fanff/coco/3dmodels/base_plate.scad

// Coco — base plate (hip MG90S pockets + Pi Zero W + wiring).
// Print floor down.
include <coco.scad>
coco_base_print();
