fanff/coco/3dmodels/coco.scad

// Coco biped — printable parts for 4× MG90S (2 per leg) + electronics deck.
// Units: millimetres. Robot frame: +X forward, +Y left, +Z up.
//
// side = +1 → left, side = −1 → right (mirror of the left solid).

include <mg90s.scad>

$fn = $fn ? $fn : 48;
eps = 0.08;

// --- layout ---
hip_span     = 72.0;   // hip shaft to hip shaft (Y)
hip_x        = 36.0;   // hip shafts forward of plate centre
leg_len      = 56.0;   // hip shaft to foot-servo shaft (Z)
wall         = 3.6;
clearance    = 0.40;

// --- foot (MG90S laid in the sole, shaft pointing backward / −X) ---
sole_t       = 4.0;
toe_reach    = 43.0;   // forward-most toe centre, from the shaft
heel_lip     = 2.0;    // keep the heel short so the shin flange clears
foot_boss_h  = 6.5;
foot_boss_d  = 22.0;
ankle_h      = MG90S_BODY_W / 2 + clearance + wall + sole_t;

// Well footprint in foot XY after mg90s_orient_foot (left foot, shaft at origin).
function coco_foot_well_xmin() = -wall;
function coco_foot_well_xmax() = mg90s_horn_z() + wall;
function coco_foot_well_ymin() = mg90s_body_xmin() - wall;
function coco_foot_well_ymax() = mg90s_body_xmax() + wall;
function coco_foot_sole_x() = (coco_foot_well_xmin() + coco_foot_well_xmax()) / 2;
function coco_foot_sole_y() = (coco_foot_well_ymin() + coco_foot_well_ymax()) / 2;
// Slight tuck under the well walls; the sole then hulls forward to the toes.
hug_inset = 2.0;
// Round window in the front socket wall (opposite the shaft). Millimetres.
front_hole_d = 4.0;
// Leg anchors in the left-foot frame (origin = output shaft, Y=0, Z=0).
// Rear: horn / shaft. Front: 4 mm window on the outer face of the well.
function coco_foot_shaft_anchor() = [0, 0, 0];
function coco_foot_mirror_hole_x() = mg90s_horn_z() + wall;
function coco_foot_mirror_anchor() = [coco_foot_mirror_hole_x(), 0, 0];
function coco_foot_mirror_peg_d() = front_hole_d - 0.40;
// Laid-down motor top (world +Z). Everything above this plane is cut away
// so the servo can slide into the well from above.
function coco_foot_motor_top_z() = MG90S_BODY_W / 2;

// Four overlapping gnome-toe blobs (flattened spheres), inboard → outboard.
// Centres are close enough that the balls collide instead of splitting.
coco_toe_x = [38.0, toe_reach, 42.0, 37.0];
coco_toe_y = [-1.5, 6.0, 13.0, 20.0];
coco_toe_d = [16.0, 15.0, 14.0, 10.0];
toe_z_scale = 0.65;   // squash the spheres in Z (a bit taller than a flat slab)

// --- leg (simple reverse-U ∩; verticals sit on the two foot anchors) ---
hip_flange_d = 26.0;
hip_flange_h = 6.5;
leg_beam_t   = 6.0;    // beam thickness (X for verticals; Z for the top bar)
leg_beam_d   = 20.0;   // beam depth along +Y (outboard of the horn plane)
leg_y0       = 2.0;    // inboard face of the beams; sits slightly outboard
// Underside of the top bar: just above the foot motor (shaft at −leg_len).
leg_top_z    = -leg_len + 10.5;
// Fore–aft span is the two anchors (shaft → 4 mm hole).
// Hip flange / rear stem omitted for now (add back when the hip attach is ready).

// --- base plate ---
plate_x      = 114.0;
plate_y      = 82.0;
floor_t      = 4.0;
rim_h        = 8.0;
rim_t        = 2.2;
hip_z        = 11.0;   // hip shaft height above plate bottom

// Pi Zero W (65 × 30), holes 58 × 23, M2.5 — sits behind the hip pods
pi_hole_dx    = 58.0;
pi_hole_dy    = 23.0;
pi_standoff_h = 6.0;
pi_standoff_d = 6.5;
pi_hole_d     = 2.7;
pi_cx         = -24.0;
pi_cy         = 0.0;

function coco_hip_y(side) = side * hip_span / 2;
function coco_hip_z_world() = ankle_h + leg_len;

module coco_rounded_rect(size, r, center = true) {
    x = size[0];
    y = size[1];
    rr = min(r, x / 2 - 0.1, y / 2 - 0.1);
    translate(center ? [0, 0] : [x / 2, y / 2])
        offset(r = rr)
            square([x - 2 * rr, y - 2 * rr], center = true);
}

module coco_label(txt, size = 6, h = 0.7) {
    linear_extrude(h)
        text(
            txt,
            size = size,
            font = "Liberation Sans:style=Bold",
            halign = "center",
            valign = "center"
        );
}

// Preview-only RGB triad (not used by printable parts).
// Robot / left-foot frame: +X forward (toes), +Y left, +Z up.
// Origin is the foot-servo output shaft; −X is the shaft / heel.
module coco_axis_arrow(len, d = 2.0) {
    fn = 16;
    cylinder(d = d, h = len, $fn = fn);
    translate([0, 0, len])
        cylinder(d1 = d * 2.4, d2 = 0.15, h = 6.5, $fn = fn);
}

module coco_axes(len = 32) {
    color("White")
        sphere(d = 4.0, $fn = 20);
    // +X forward (toes)
    color("Red") {
        rotate([0, 90, 0])
            coco_axis_arrow(len);
        translate([len + 10, -7, 6])
            coco_label("+X", size = 6, h = 1.4);
    }
    // −X shaft / heel (shorter)
    color("Maroon") {
        rotate([0, -90, 0])
            coco_axis_arrow(len * 0.42);
        translate([-(len * 0.42 + 10), -7, 6])
            coco_label("-X", size = 5, h = 1.4);
    }
    // +Y left (outboard on the left foot)
    color("LimeGreen") {
        rotate([-90, 0, 0])
            coco_axis_arrow(len);
        translate([7, len + 10, 6])
            coco_label("+Y", size = 6, h = 1.4);
    }
    // +Z up
    color("DodgerBlue") {
        coco_axis_arrow(len);
        translate([8, 7, len + 10])
            coco_label("+Z", size = 6, h = 1.4);
    }
}

// Preview markers for the two U-leg attach points (not printable).
module coco_foot_anchor_markers() {
    module pin(col) {
        color(col) {
            sphere(d = 3.6, $fn = 20);
            rotate([0, 90, 0])
                cylinder(d = 1.6, h = 14, center = true, $fn = 16);
        }
    }
    translate(coco_foot_shaft_anchor())
        pin("Orange");
    translate(coco_foot_mirror_anchor())
        pin("Magenta");
}

// Manifold L/R stamps for soles (font text can leave a detached CGAL chip).
module coco_stamp_L(h = 1.2) {
    linear_extrude(h) {
        translate([-2.4, -3.2])
            square([1.7, 6.4]);
        translate([-2.4, -3.2])
            square([5.2, 1.7]);
    }
}

module coco_stamp_R(h = 1.2) {
    linear_extrude(h) {
        translate([-2.4, -3.2])
            square([1.7, 6.4]);
        translate([-2.4, 1.8])
            square([4.8, 1.6]);
        translate([-2.4, -0.4])
            square([4.4, 1.6]);
        translate([1.5, -0.4])
            square([1.6, 3.8]);
        translate([0.8, -3.2])
            square([1.7, 2.9]);
    }
}

module coco_stamp_lr(side = 1, h = 1.2) {
    if (side > 0)
        coco_stamp_L(h = h);
    else
        coco_stamp_R(h = h);
}

// Solid envelope used before subtracting mg90s_pocket().
module coco_servo_cage_solid(pad = 3.2) {
    translate([
        mg90s_body_xmin() - pad,
        -MG90S_BODY_W / 2 - pad,
        -pad
    ])
        cube([
            MG90S_BODY_L + 2 * pad,
            MG90S_BODY_W + 2 * pad,
            mg90s_horn_z() + pad
        ]);
}

// World +Z hatch so a servo drops in from above. dir matches mg90s_orient_shaft_y.
module coco_servo_hatch(dir = 1) {
    translate([
        (mg90s_body_xmin() + mg90s_body_xmax()) / 2,
        dir * MG90S_BODY_W / 2 + dir * 8,
        MG90S_BODY_H / 2
    ])
        cube([MG90S_BODY_L + 1.2, 16, MG90S_BODY_H + 6], center = true);
}

// =====================================================================
// Foot — MG90S lives in the sole, laid down, shaft pointing backward (−X).
// 180° about that shaft (world X) vs the previous pose: cable inboard,
// shaft hole at the heel and 4 mm window still coaxial on X.
// Origin: output shaft. Horn plane is YZ at x = 0 (horn toward −X).
// Body occupies +X (forward). Print sole-down.
// The well is sliced at the motor top (world +Z = BODY_W/2) so the servo
// slides in from above; nothing green sits above that plane.
// The ground plate is a compact gnome foot: short heel (shin clearance),
// a little margin around the motor, four overlapping flattened-sphere toes.
// =====================================================================

// Axis-aligned rounded outline of the motor well in foot XY.
module coco_foot_well_2d() {
    w = coco_foot_well_xmax() - coco_foot_well_xmin();
    d = coco_foot_well_ymax() - coco_foot_well_ymin();
    translate([coco_foot_sole_x(), coco_foot_sole_y()])
        coco_rounded_rect([w, d], r = 4);
}

// Pad under the well only (heel clipped). Used to keep the socket walls
// hugging the motor instead of flaring out along the toe plate.
module coco_foot_well_pad_2d() {
    w = coco_foot_well_xmax() - coco_foot_well_xmin() - 2 * hug_inset;
    d = coco_foot_well_ymax() - coco_foot_well_ymin() - 2 * hug_inset;
    intersection() {
        translate([coco_foot_sole_x(), coco_foot_sole_y()])
            coco_rounded_rect([w, d], r = 5);
        translate([heel_lip - 1, -40])
            square([90, 80]);
    }
}

// Ground plate: well pad hulled forward to the toes so the sole is one
// piece from the motor housing to the gnome balls. Left foot; right is Y-mirrored.
module coco_foot_sole_2d() {
    hull() {
        coco_foot_well_pad_2d();
        // Forefoot plate under the balls (not a matching disk per toe,
        // which made a coplanar kiss with the sphere cuts).
        for (i = [0 : 3])
            translate([coco_toe_x[i] - 4, coco_toe_y[i]])
                circle(d = coco_toe_d[i] * 0.70);
    }
}

// Flattened sphere sitting on the sole bed, overlapping its neighbours.
// Sunk into the plate so the union is a volume, not a tangent kiss.
module coco_foot_toe_ball(i) {
    r = coco_toe_d[i] / 2;
    translate([coco_toe_x[i], coco_toe_y[i], r * toe_z_scale - 1.0])
        scale([1, 1, toe_z_scale])
            sphere(d = coco_toe_d[i]);
}

module coco_foot_positive() {
    sole_z = -ankle_h;
    union() {
        translate([0, 0, sole_z]) {
            linear_extrude(sole_t)
                coco_foot_sole_2d();
            for (i = [0 : 3])
                coco_foot_toe_ball(i);
        }
        // Well walls hug the motor; they hull only onto the well pad, not
        // the toe plate, so the socket does not flare toward the toes.
        hull() {
            mg90s_orient_foot()
                coco_servo_cage_solid(pad = wall);
            translate([0, 0, sole_z + 0.3])
                linear_extrude(sole_t - 0.3)
                    coco_foot_well_pad_2d();
        }
    }
}

// Open-top slot at the cable end so the lead drops in with the servo.
// After the 180° X-flip, local −Y is world +Z, so the cube runs up
// through the motor-top plane and out the wall (local −X / inboard).
module coco_foot_wire_notch() {
    nw = 8.0;
    translate([
        mg90s_body_xmin() - 28,
        -20.0,
        -1.0
    ])
        cube([26, 24, nw]);
}

// Round window in the front socket wall, opposite the shaft (−X / heel).
// Coaxial with the output shaft; diameter is `front_hole_d`.
module coco_foot_front_hole() {
    translate([coco_foot_mirror_hole_x() - wall - 2, 0, 0])
        rotate([0, 90, 0])
            cylinder(d = front_hole_d, h = wall + 8);
}

module coco_foot_cuts() {
    sole_z = -ankle_h;
    mg90s_orient_foot()
        union() {
            mg90s_pocket(clearance = clearance, extra_shaft = 18, extra_cable = 4);
            mg90s_tab_screws(d = 2.2, h = 36);
            coco_foot_wire_notch();
        }
    coco_foot_front_hole();
    // Slice at the motor top: remove all green plastic above this plane.
    translate([0, 0, coco_foot_motor_top_z() + 50])
        cube([200, 200, 100], center = true);
    // Open the heel above the sole so the shin flange can sit on the horn.
    translate([-12, 0, 6])
        cube([24, foot_boss_d + 10, 32], center = true);
    // Zip-tie across the foot (world Y), under the body.
    translate([mg90s_horn_z() * 0.45, coco_foot_sole_y(), -MG90S_BODY_W / 2 - 0.8])
        rotate([90, 0, 0])
            cylinder(d = 3.4, h = 80, center = true);
    // Inset tread on the mid-sole (not the toe balls — offset would pinch them).
    translate([0, 0, sole_z])
        intersection() {
            translate([0, 0, -0.2])
                linear_extrude(2.0)
                    coco_foot_sole_2d();
            for (x = [10, 18, 26, 34])
                translate([x, coco_foot_sole_y(), 0.85])
                    cube([3.0, 16, 1.8], center = true);
        }
    // Flatten anything that dipped below the sole bed (sphere bottoms).
    translate([0, 0, sole_z - 50])
        cube([200, 200, 100], center = true);
}

module coco_foot(side = 1) {
    difference() {
        mirror([0, side < 0 ? 1 : 0, 0])
            coco_foot_positive();
        mirror([0, side < 0 ? 1 : 0, 0])
            coco_foot_cuts();
    }
}

// =====================================================================
// Leg — simple reverse-U shin (∩)
// Origin: hip shaft, horn plane at y = 0.
// Two vertical posts drop to the foot anchors; a top bar joins them:
//   rear  = shaft plane (x = 0); round horn flange omitted for now
//   front = 4 mm mirror hole (x = coco_foot_mirror_hole_x())
// Beams live on the +Y (outboard) side of the horn plane; a short stub
// on the front post reaches y = 0 for the peg.
// Hip flange, rear stem, and rear round horn boss are left off for now.
// =====================================================================
function coco_u_x_aft() = coco_foot_shaft_anchor()[0];
function coco_u_x_fore() = coco_foot_mirror_hole_x();

// Vertical post centred on x, from z_lo to z_hi, occupying y = [leg_y0, leg_y0+d].
module coco_leg_post(x, z_lo, z_hi) {
    translate([x - leg_beam_t / 2, leg_y0, z_lo])
        cube([leg_beam_t, leg_beam_d, z_hi - z_lo]);
}

module coco_leg_positive() {
    x0 = coco_u_x_aft();
    x1 = coco_u_x_fore();
    z_foot = -leg_len;
    z_bar = leg_top_z;
    peg_boss_h = leg_beam_t / 2 + 1.0;
    union() {
        // Top bar of the reverse U (low over the foot, extending +Y).
        translate([x0 - leg_beam_t / 2, leg_y0, z_bar])
            cube([(x1 - x0) + leg_beam_t, leg_beam_d, leg_beam_t]);
        // Rear vertical at the shaft plane (no round horn boss yet).
        coco_leg_post(x0, z_foot + 2, z_bar + leg_beam_t);
        // Front vertical → 4 mm peg.
        coco_leg_post(x1, z_foot + 2, z_bar + leg_beam_t);
        // Front foot anchor: short boss + peg into the 4 mm window.
        hull() {
            translate([x1 - leg_beam_t / 2, leg_y0, z_foot + 2])
                cube([leg_beam_t, leg_beam_d, 10]);
            translate([x1, 0, z_foot])
                rotate([0, 90, 0])
                    cylinder(d = 11, h = peg_boss_h);
        }
        // Overlap the peg into the boss so the union stays one volume.
        translate([x1 + peg_boss_h - 0.6, 0, z_foot])
            rotate([0, -90, 0])
                cylinder(d = coco_foot_mirror_peg_d(), h = peg_boss_h + wall + 0.6);
    }
}

module coco_leg_cuts() {
    // Flatten the ankle so it stays above the sole.
    translate([0, 0, -leg_len - 40 - 9])
        cube([80, 80, 80], center = true);
}

module coco_leg(side = 1) {
    difference() {
        mirror([0, side < 0 ? 1 : 0, 0])
            coco_leg_positive();
        mirror([0, side < 0 ? 1 : 0, 0])
            coco_leg_cuts();
        // L/R stamp on the outboard face of the front post.
        translate([
            coco_u_x_fore() + leg_beam_t / 2 + 0.15,
            side * (leg_y0 + leg_beam_d - 0.15),
            -leg_len * 0.55
        ])
            rotate([0, side > 0 ? -90 : 90, 0])
                coco_stamp_lr(side, h = 1.8);
    }
}

// =====================================================================
// Base plate — hip servos + Pi Zero W + BEC / battery tie-downs
// Origin: plate centre, z = 0 at the bottom of the floor.
// =====================================================================
module coco_hip_pod_solid(side) {
    translate([hip_x, coco_hip_y(side), hip_z])
        mg90s_orient_shaft_y(side)
            coco_servo_cage_solid(pad = wall);
}

module coco_hip_pod_cut(side) {
    translate([hip_x, coco_hip_y(side), hip_z])
        mg90s_orient_shaft_y(side)
            union() {
                mg90s_pocket(clearance = clearance, extra_shaft = 16);
                mg90s_tab_screws(d = 2.2, h = 28);
                coco_servo_hatch(dir = side);
            }
}

module coco_pi_standoffs() {
    for (sx = [-1, 1], sy = [-1, 1]) {
        translate([
            pi_cx + sx * pi_hole_dx / 2,
            pi_cy + sy * pi_hole_dy / 2,
            floor_t - 1.2
        ])
            difference() {
                cylinder(d = pi_standoff_d, h = pi_standoff_h + 1.2);
                translate([0, 0, -eps])
                    cylinder(d = pi_hole_d, h = pi_standoff_h + 2.0);
            }
    }
}

module coco_base_plate() {
    difference() {
        union() {
            linear_extrude(floor_t)
                coco_rounded_rect([plate_x, plate_y], r = 6);
            difference() {
                linear_extrude(rim_h)
                    coco_rounded_rect([plate_x, plate_y], r = 6);
                translate([0, 0, -eps])
                    linear_extrude(rim_h + 2 * eps)
                        coco_rounded_rect(
                            [plate_x - 2 * rim_t, plate_y - 2 * rim_t],
                            r = 5
                        );
            }
            coco_hip_pod_solid(1);
            coco_hip_pod_solid(-1);
            coco_pi_standoffs();
            for (s = [-1, 1])
                translate([pi_cx + 6, s * 24, floor_t - 0.4])
                    cube([24, 15, 1.6], center = true);
        }
        coco_hip_pod_cut(1);
        coco_hip_pod_cut(-1);
        // extra world-+Z hatches so each hip roof is fully open
        for (s = [-1, 1])
            translate([hip_x - 2, coco_hip_y(s) - s * 14, hip_z + 10])
                cube([24, 18, 16], center = true);
        for (sx = [-1, 1], sy = [-1, 1])
            translate([
                pi_cx + sx * pi_hole_dx / 2,
                pi_cy + sy * pi_hole_dy / 2,
                -eps
            ])
                cylinder(d = pi_hole_d, h = floor_t + pi_standoff_h + 1);
        // 2S pack straps under the Pi
        for (sx = [-1, 1], sy = [-1, 1])
            translate([pi_cx + sx * 16, sy * 14, floor_t / 2])
                cube([12, 2.2, 3.4], center = true);
        // hip-wire wells toward GPIO
        for (s = [-1, 1])
            translate([hip_x - 20, s * 10, -eps])
                cylinder(d = 6.5, h = floor_t + 2);
        // ankle-wire holes at the Y rim, beside each hip shaft
        for (s = [-1, 1])
            translate([hip_x - 8, s * (plate_y / 2 - 5), -eps])
                cylinder(d = 5.5, h = rim_h + 2);
        // cable well between the hip pods
        translate([hip_x - 8, 0, -eps])
            linear_extrude(floor_t + 2)
                coco_rounded_rect([14, 16], r = 3);
        translate([pi_cx + 4, 0, floor_t - 0.35])
            coco_label("COCO", size = 6, h = 0.55);
        // flatten anything that dipped below the bed
        translate([0, 0, -50])
            cube([plate_x + 20, plate_y + 20, 100], center = true);
    }
}

module coco_foot_print(side = 1) {
    translate([0, 0, ankle_h])
        coco_foot(side);
}

module coco_leg_print(side = 1) {
    // Flat on the bed: reverse-U in the XY print plane, outboard face up.
    // Front peg boss is a d=11 disk at y = 0; beams sit further +Y.
    y_lo = side > 0 ? -5.5 : -(leg_y0 + leg_beam_d);
    translate([0, 0, -y_lo])
        rotate([90, 0, 0])
            coco_leg(side);
}

module coco_base_print() {
    coco_base_plate();
}
