fanff/coco/3dmodels/foot_left.scad

// Coco — left foot (print sole down). Open MG90S well in the sole.
include <coco.scad>
coco_foot_print(side = 1);
