fanff/coco/iv.py

iv=[90,80,64,90]

# BCM GPIO for pigpio (index order: feetL, feetR, hipR, hipL)
servoGpios = [17, 18, 27, 22]

LEFTFEET=0
RIGHTFEET=1
LEFTHIP=3
RIGHTHIP=2

nameMap = {
	"feetL":LEFTFEET,
	"feetR":RIGHTFEET,
	"hipL":LEFTHIP,
	"hipR":RIGHTHIP,
}
